mikebebjak/M.2-GNSS-Card/EDA/M.2-Card-Footprints-main/preview.png

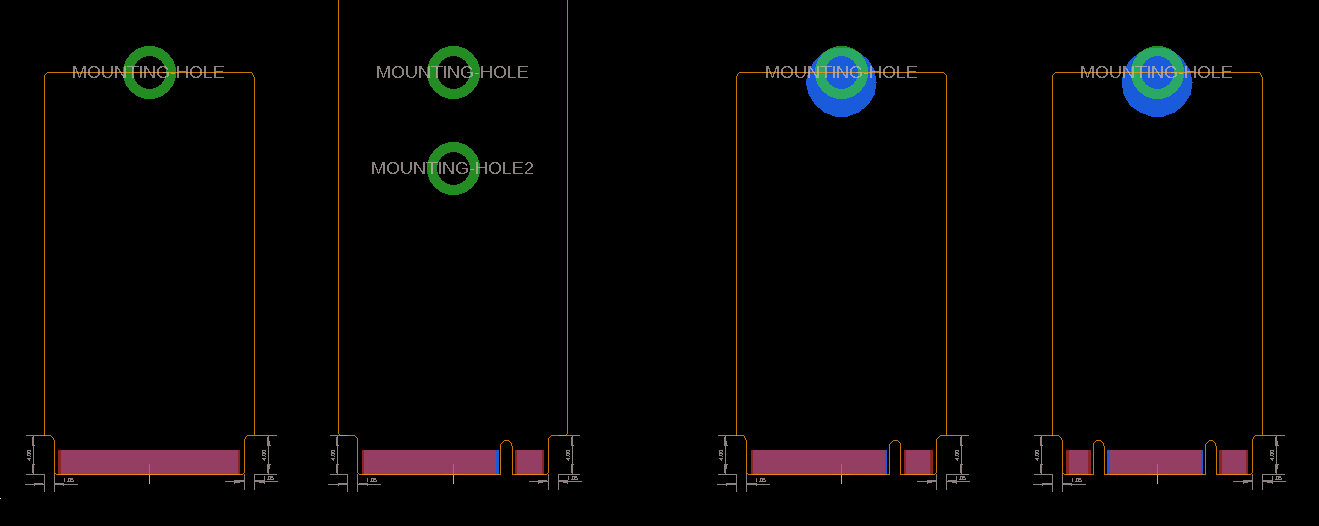
EDA/M.2-Card-Footprints-main/preview.png
